yosihisa/CanSat2020/firmware/CubeIDE/sub/Inc/_Setting.h

/*
 * _Setting.h
 *
 *  Created on: Nov 3, 2019
 *      Author: yosihisa
 */

#ifndef SETTING_H_
#define SETTING_H_

#define RESOLUTION VGA


//------ゴール-----
//色相の範囲
#define G_H_MIN_1 0
#define G_H_MAX_1 10

#define G_H_MIN_2 330
#define G_H_MAX_2 360

//彩度の範囲
#define G_S_MIN 115
#define G_S_MAX 256

//明度の範囲
#define G_V_MIN 77
#define G_V_MAX 256

//------パラシュート-----
//色相の範囲
#define P_H_MIN_1 0	
#define P_H_MAX_1 10

#define P_H_MIN_2 330
#define P_H_MAX_2 360

//彩度の範囲
#define P_S_MIN 115
#define P_S_MAX 256

//明度の範囲
#define P_V_MIN 77
#define P_V_MAX 256

#define HEIGHT 480
#define WIDTH  640

#endif /* SETTING_H_ */
